mi3nts/canopy/res/canopyPowerDiagram.drawio.png

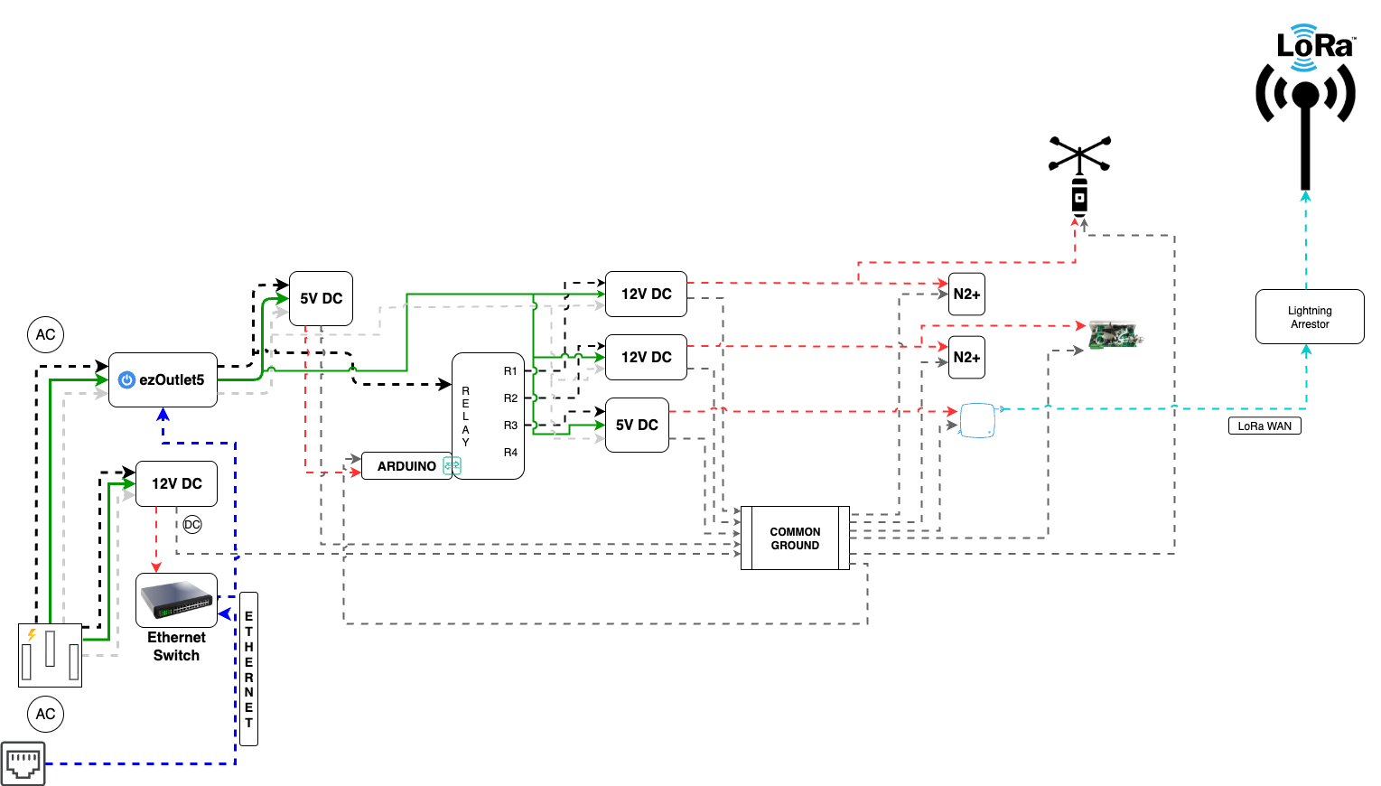
res/canopyPowerDiagram.drawio.png
