mi3nts/canopy/res/lightModule.drawio.png

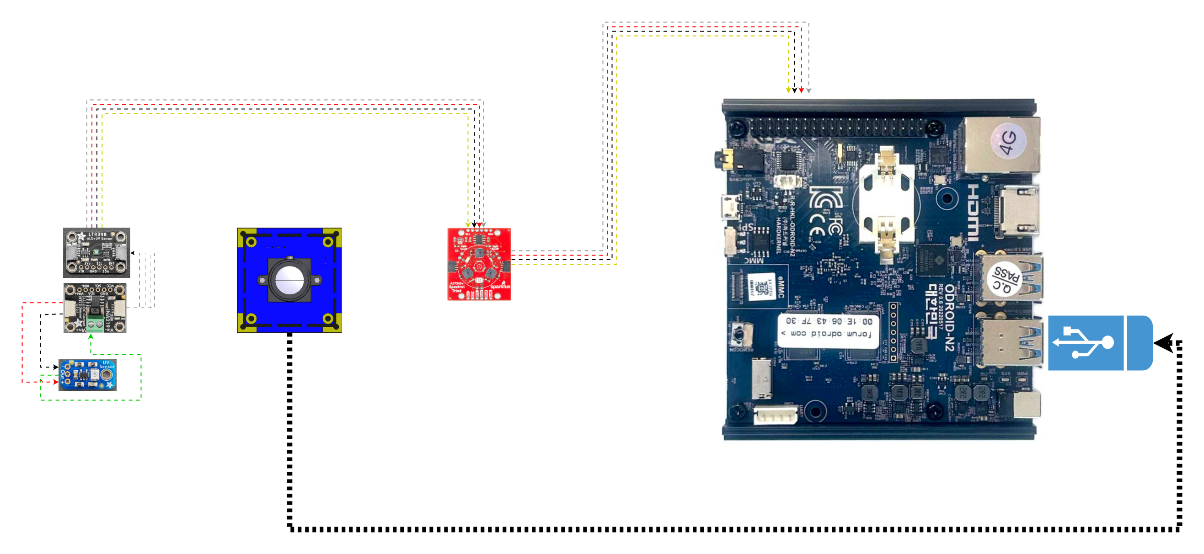
res/lightModule.drawio.png
