mi3nts/canopy/firmware/xu4Mqtt/pcbFirmware/orangepi/dreamBme280Reader.py

#!/usr/bin/python
# ***************************************************************************
#   I2CPythonMints
#   ---------------------------------
#   Written by: Lakitha Omal Harindha Wijeratne
#   - for -
#   MINTS :  Multi-scale Integrated Sensing and Simulation
#     & 
#   TRECIS: Texas Research and Education Cyberinfrastructure Services
#
#   ---------------------------------
#   Date: July 7th, 2022
#   ---------------------------------
#   This module is written for generic implimentation of MINTS projects
#   --------------------------------------------------------------------------
#   https://github.com/mi3nts
#   https://trecis.cyberinfrastructure.org/
#   http://utdmints.info/
#  ***************************************************************************



import sys
import time
import os
import smbus2
#from i2cMints.i2c_scd30 import SCD30
from i2cMints.i2c_bme280v3 import BME280V3
#from i2cMints.i2c_tmp117 import TMP117
#from i2cMints.i2c_cht8305c import CHT8305C
from collections import OrderedDict
from mintsXU4 import mintsSensorReader as mSR
from mintsPMCorrections import corrections as corr

debug        = False 
bus4          = smbus2.SMBus(4) #Busses 4 and 3 for Orange Pi Dream Board
bus3          = smbus2.SMBus(3) #Busses 4 and 3 for Orange Pi Dream Board

# # BME280V3
bme280v3_bus4     = BME280V3(bus4,debug)
bme280v3_bus3     = BME280V3(bus3,debug)
sensor4	     = "BME280V3_2"
sensor3      = "BME280V3"
# # TMP117
# tmp117      = TMP117(bus,debug) 
 
# CHT8305C
#cht8305c    = CHT8305C(bus,debug) 

checkTrials  = 0
loopInterval = 5 

def main(loopInterval):
    bme280v3_valid4   = bme280v3_bus4.initiate(30)
    bme280v3_valid3   = bme280v3_bus3.initiate(30)
    # tmp117_valid     = tmp117.initiate(30)
    # cht8305c_valid   = cht8305c.initiate()
    startTime    = time.time()
    while True:
        try:
            print("======= BME280V3 ========")
            if bme280v3_valid4:
                raw_data4 = bme280v3_bus4.read()
                climate_dict = OrderedDict([
                    ("dateTime"    , raw_data4[0]),
                    ("humidity"    , float(raw_data4[1])),
                    ("pressure"    , float(raw_data4[2]) / 100),
                    ("temperature" , float(raw_data4[3])),
                    ("dewPoint"    , float(raw_data4[4]))
                ])
                corr.writeJSONLatestClimate(climate_dict,sensor4)
                mSR.BME280V3WriteI2cDREAM(raw_data4, sensor4)
            if bme280v3_valid3:
                raw_data3 = bme280v3_bus3.read()
                climate_dict = OrderedDict([
                    ("dateTime"    , raw_data3[0]),
                    ("humidity"    , float(raw_data3[1])),
                    ("pressure"    , float(raw_data3[2]) / 100),
                    ("temperature" , float(raw_data3[3])),
                    ("dewPoint"    , float(raw_data3[4]))
                ])
                corr.writeJSONLatestClimate(climate_dict,sensor3)
                mSR.BME280V3WriteI2cDREAM(raw_data3, sensor3)
            time.sleep(1)     
            
            # print("======= TMP117 ========")
            # if tmp117_valid:
            #     mSR.TMP117WriteI2c(tmp117.read())
            # time.sleep(1)       

            # print("======= CHT8305C ========")
            # if cht8305c_valid:
            #      mSR.CHT8305CWriteI2c(cht8305c.read())
            # time.sleep(1)     
            
            startTime = mSR.delayMints(time.time() - startTime,loopInterval)
            

        except Exception as e:
            print(e)
            time.sleep(10)
        
if __name__ == "__main__":
    print("=============")
    print("    MINTS    ")
    print("=============")
    print("Monitoring Climate data for Minty Cube")
    main(loopInterval)
